naoya1110/sound_remocon/v2/ltspice/mixer_circuit_simulation.asc

C1: cap; 1µ
C2: cap; 1µ
C3: cap; 1µ
C4: cap; 0.001µ
C5: cap; 4.7µ
C6: cap; 1µ
C7: cap; 1µ
C8: cap; 1µ
R1: res; 5k
R2: res; 1k
R3: res; 10k
R4: res; 10k
R5: res; 10k
R6: res; 10k
R7: res; 10k
R8: res; 100k
R9: res; 5k
R10: res; 1k
R11: res; 10k
R12: res; 5k
R13: res; 1k
R14: res; 10k
R15: res; 10k
R16: res; 10k
R17: res; 5k
R18: res; 1k
R19: res; 10k
R20: res; 5k
R21: res; 1k
R22: res; 10k
R23: res; 5k
R24: res; 1k
R25: res; 10k
U1: OP07
U2: OP07
V1: voltage; 5
V2: voltage; PULSE(0 3.3 0 0 0 0.833m 1.666m)
V3: voltage; PULSE(0 3.3 0 0 0 0.714m 1.428m)
V4: voltage; PULSE(0 3.3 0 0 0 0.625m 1.25m)
V5: voltage; PULSE(0 3.3 0 0 0 1m 2m)
V6: voltage; PULSE(0 3.3 0 0 0 0.555m 1.111m)
V7: voltage; PULSE(0 3.3 0 0 0 1.25m 2.5m)
Named nets: 0, output
.tran 3
